SunHanGP/X-TRACK/Software/X-Track/USER/HAL/HAL.cpp

#include "HAL.h"
#include "App/Version.h"
#include "MillisTaskManager/MillisTaskManager.h"

static MillisTaskManager taskManager;

static bool HAL_I2C_Init()
{
    if(HAL::I2C_Scan() <= 0)
    {
        Serial.println("I2C: disable sensors");
        return false;
    }
    return true;
}

#if CONFIG_SENSOR_ENABLE

static void HAL_Sensor_Init()
{

#if CONFIG_SENSOR_IMU_ENABLE
    if(HAL::IMU_Init())
    {
        taskManager.Register(HAL::IMU_Update, 1000);
    }
#endif

#if CONFIG_SENSOR_MAG_ENABLE
    if(HAL::MAG_Init())
    {
        taskManager.Register(HAL::MAG_Update, 1000);
    }
#endif
}

#endif

static void HAL_TimerInterrputUpdate()
{
#if !CONFIG_LIPO_FUEL_GAUGE_ENABLE
    HAL::Power_Update();
#endif
    HAL::Encoder_Update();
    HAL::Audio_Update();
}

void HAL::HAL_Init()
{
    Serial.begin(115200);
    Serial.println(VERSION_FIRMWARE_NAME);
    Serial.println("Version: " VERSION_SOFTWARE);
    Serial.println("Author: "  VERSION_AUTHOR_NAME);
    Serial.println("Project: " VERSION_PROJECT_LINK);
    
#if CONFIG_SENSOR_ENABLE
    bool hasI2CDevice = HAL_I2C_Init();
#endif

    FaultHandle_Init();

#if CONFIG_SHOW_STACK_INFO | CONFIG_SHOW_HEAP_INFO
    Memory_DumpInfo();
#endif

    Power_Init();
    Backlight_Init();
    Encoder_Init();
    Clock_Init();
    Buzz_init();
    GPS_Init();
#if CONFIG_SENSOR_ENABLE
    if(hasI2CDevice){
        HAL_Sensor_Init();
    }
#endif
    Audio_Init();
    SD_Init();

    Display_Init();

#if CONFIG_WATCH_DOG_ENABLE
    uint32_t timeout = WDG_Init(CONFIG_WATCH_DOG_TIMEOUT);
    taskManager.Register(WDG_ReloadCounter, CONFIG_WATCH_DOG_TIMEOUT / 10);
    Serial.printf("WatchDog: Timeout = %dms\r\n", timeout);
#endif

    taskManager.Register(Power_EventMonitor, 100);
    taskManager.Register(GPS_Update, 200);
    taskManager.Register(SD_Update, 500);

#if CONFIG_SHOW_STACK_INFO | CONFIG_SHOW_HEAP_INFO
    taskManager.Register(Memory_DumpInfo, 1000);
#endif
    
#if CONFIG_LIPO_FUEL_GAUGE_ENABLE
    taskManager.Register(Power_Update, 500);
#endif
    Timer_SetInterrupt(CONFIG_HAL_UPDATE_TIM, 10 * 1000, HAL_TimerInterrputUpdate);
    Timer_SetEnable(CONFIG_HAL_UPDATE_TIM, true);
}

void HAL::HAL_Update()
{
    taskManager.Running(millis());
}
